ukmaker/nindasgym/assets/IMG_1002.jpg

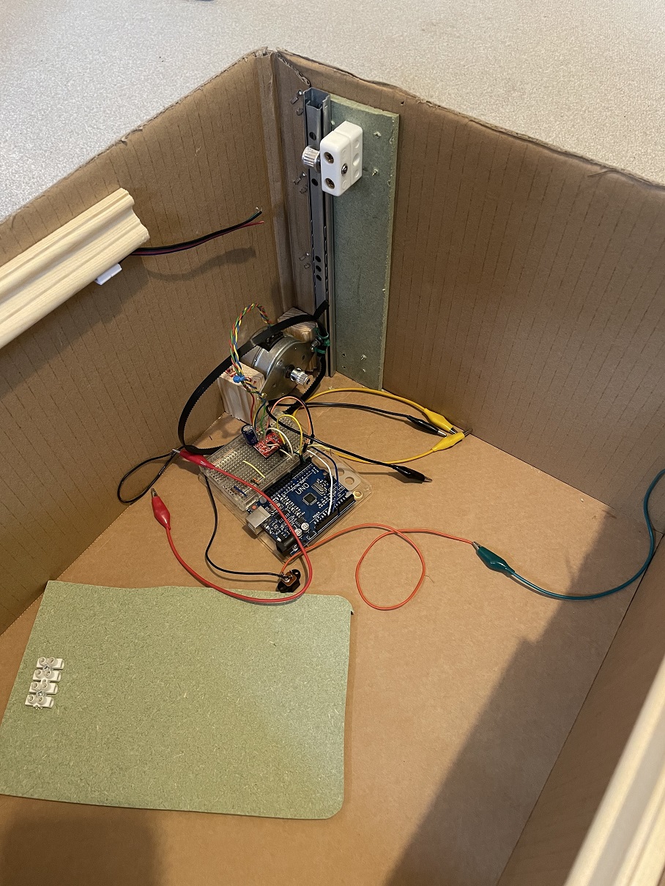
assets/IMG_1002.jpg
