ukmaker/nindasgym/assets/IMG_1003.jpg

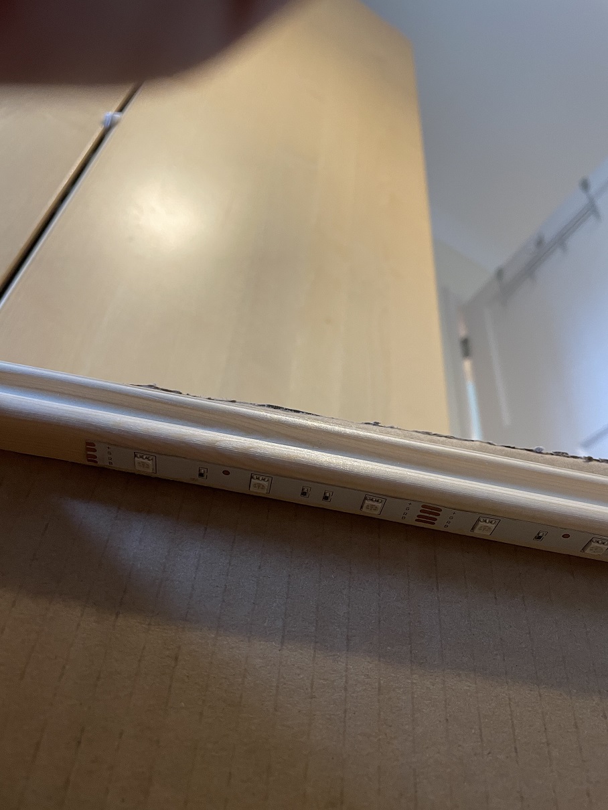
assets/IMG_1003.jpg
