ukmaker/nindasgym/assets/IMG_1004.jpg

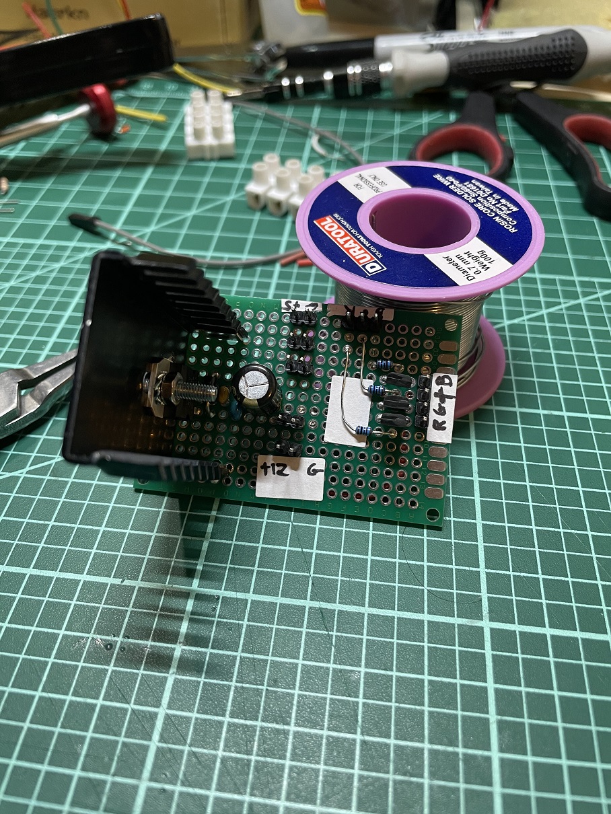
assets/IMG_1004.jpg
