ukmaker/nindasgym/assets/IMG_1005.jpg

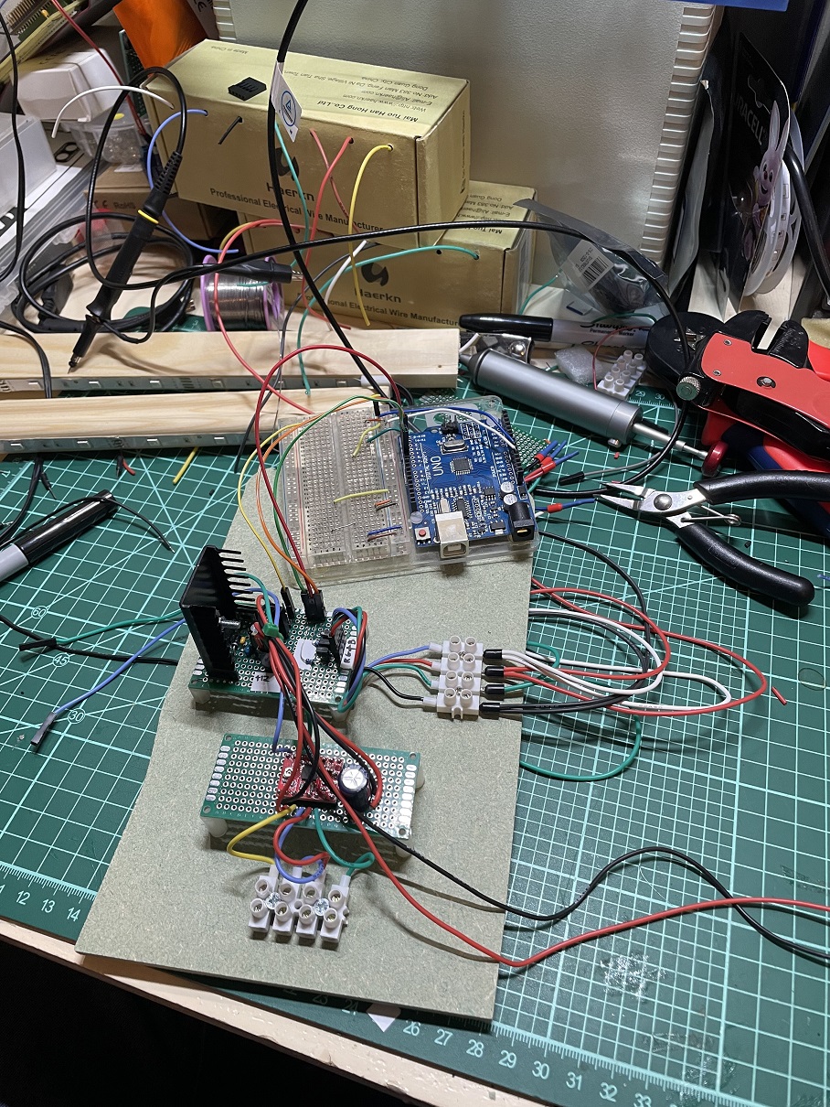
assets/IMG_1005.jpg
