ukmaker/nindasgym/assets/IMG_1007.jpg

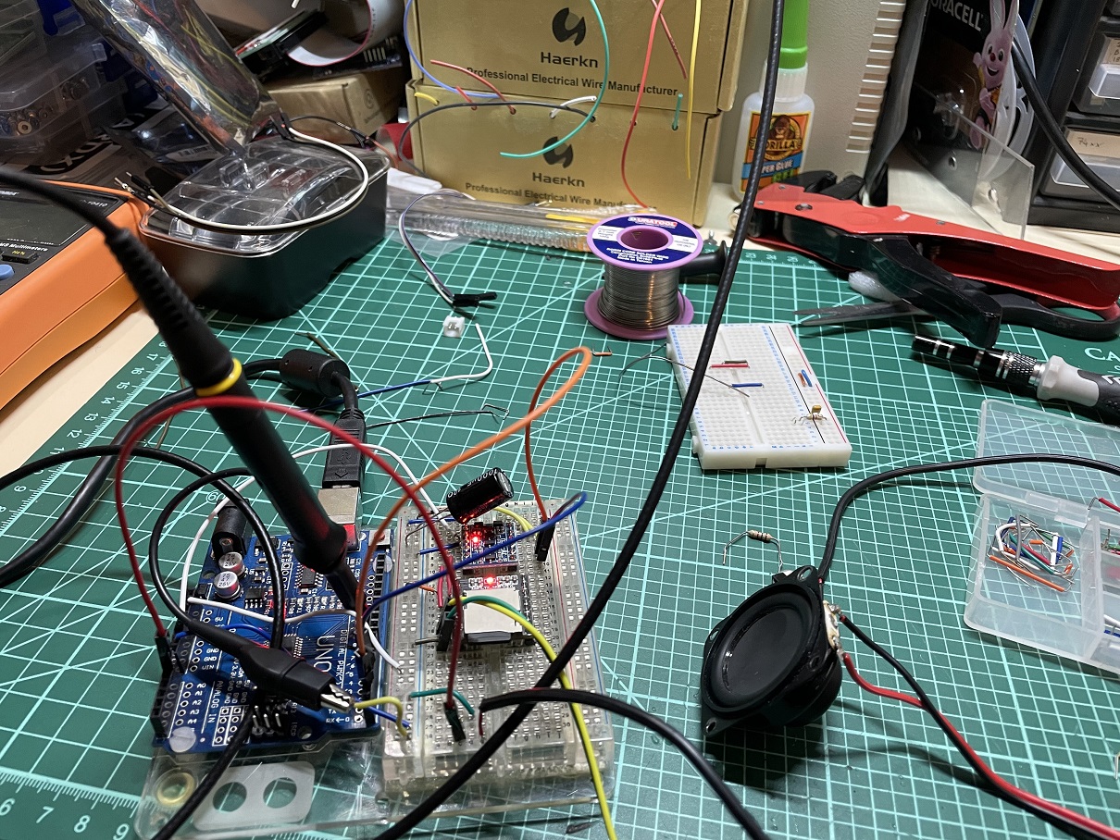
assets/IMG_1007.jpg
