ukmaker/nindasgym/assets/IMG_1008.jpg

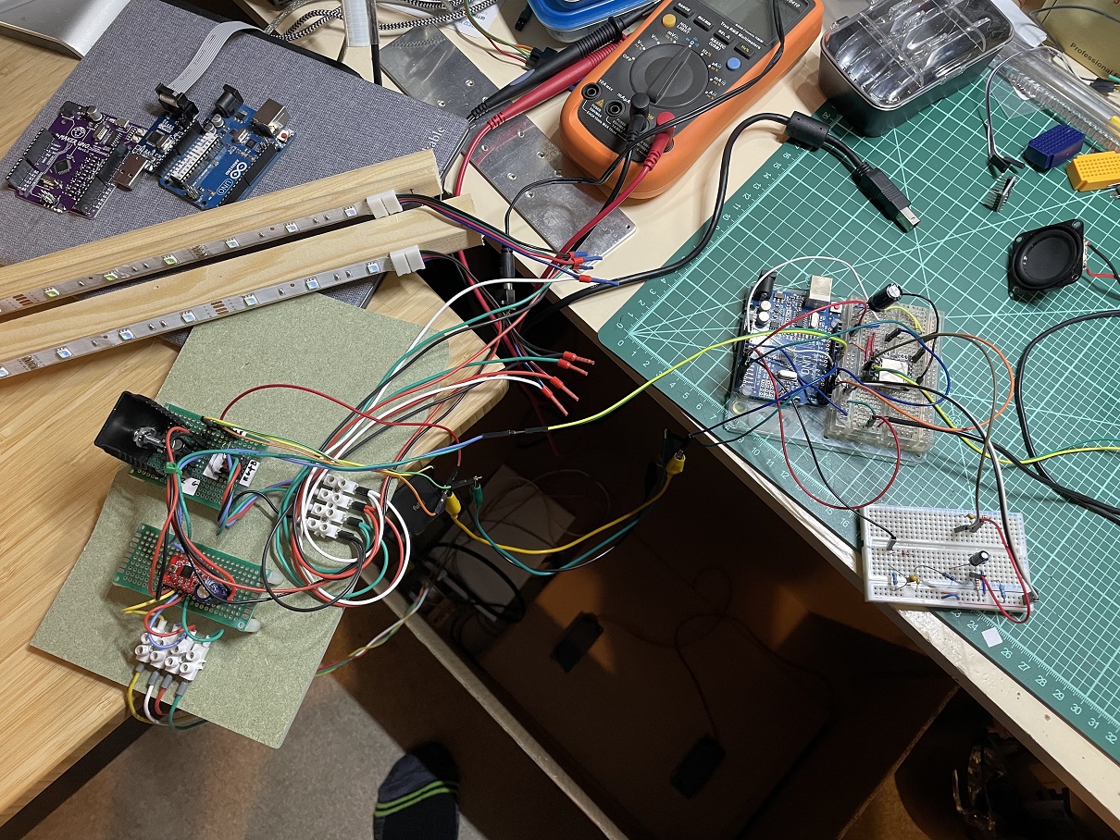
assets/IMG_1008.jpg
