ukmaker/nindasgym/assets/IMG_1011.jpg

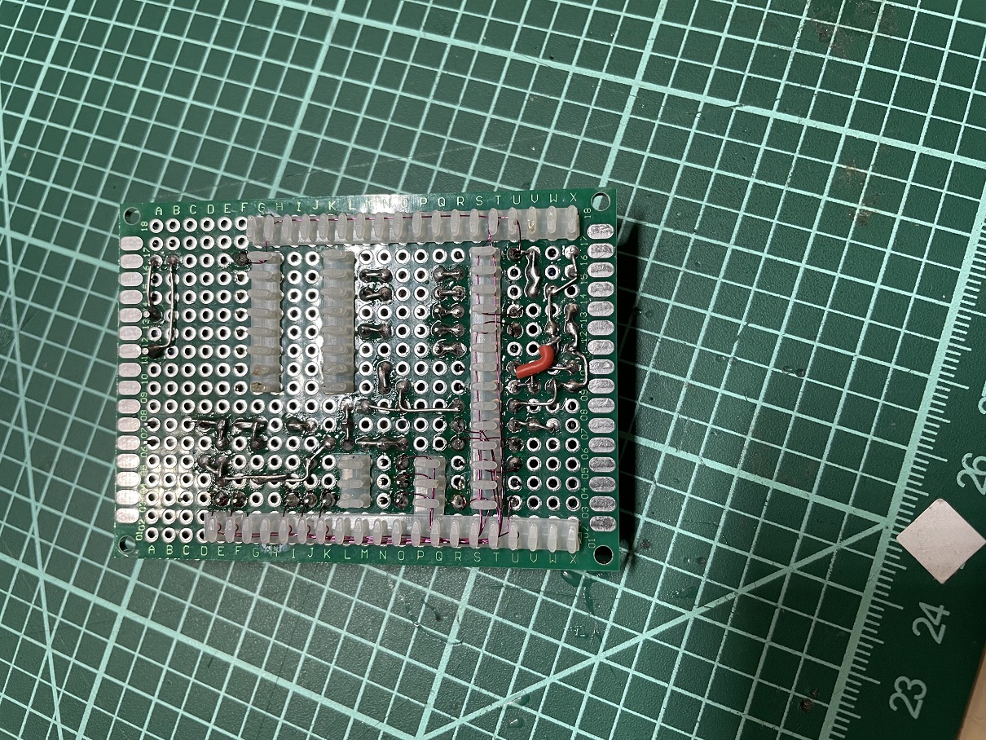
assets/IMG_1011.jpg
