ukmaker/nindasgym/assets/IMG_1012.jpg

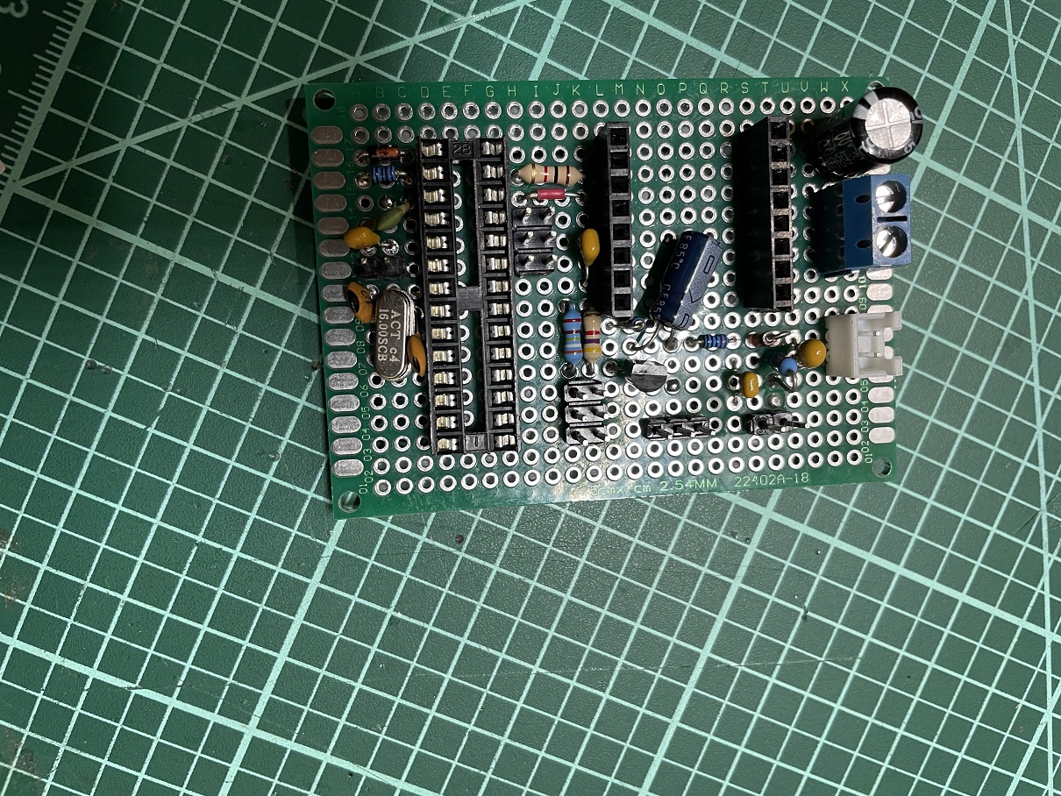
assets/IMG_1012.jpg
