ukmaker/nindasgym/assets/IMG_1013.jpg

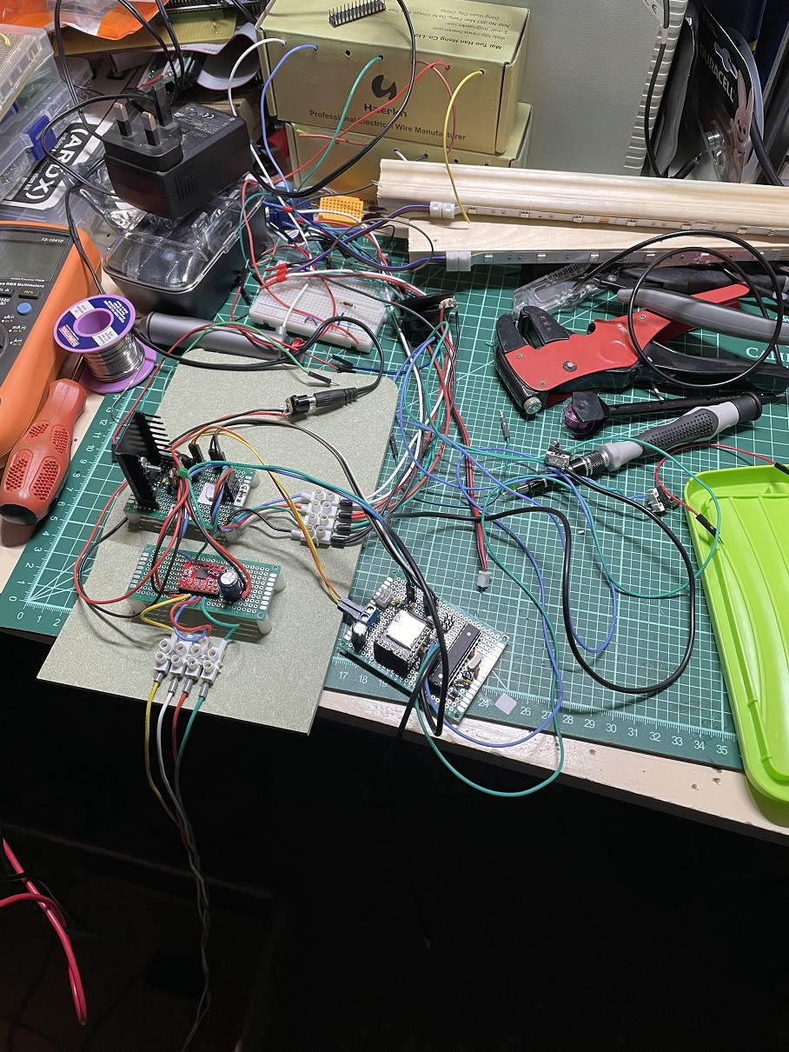
assets/IMG_1013.jpg
