ukmaker/nindasgym/assets/IMG_1023.JPG

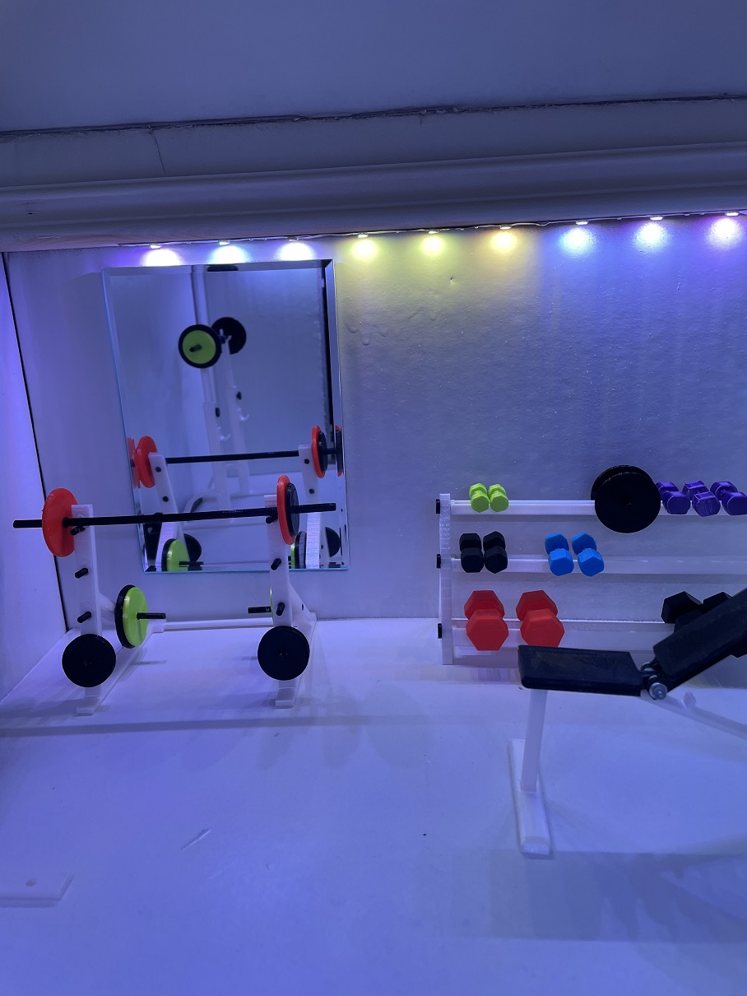
assets/IMG_1023.JPG
