ukmaker/nindasgym/assets/IMG_1027.JPG

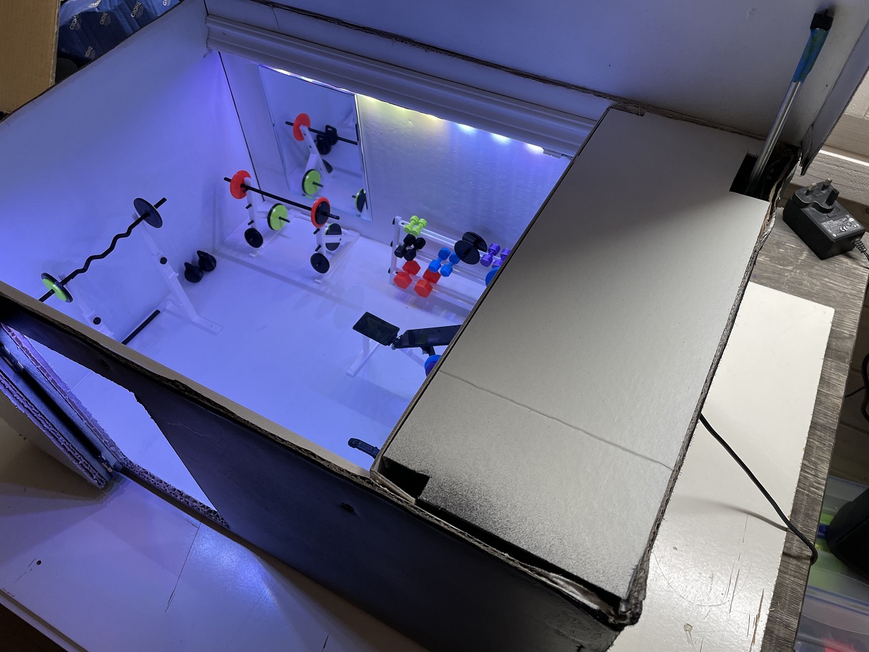
assets/IMG_1027.JPG
