ukmaker/nindasgym/assets/IMG_1028.JPG

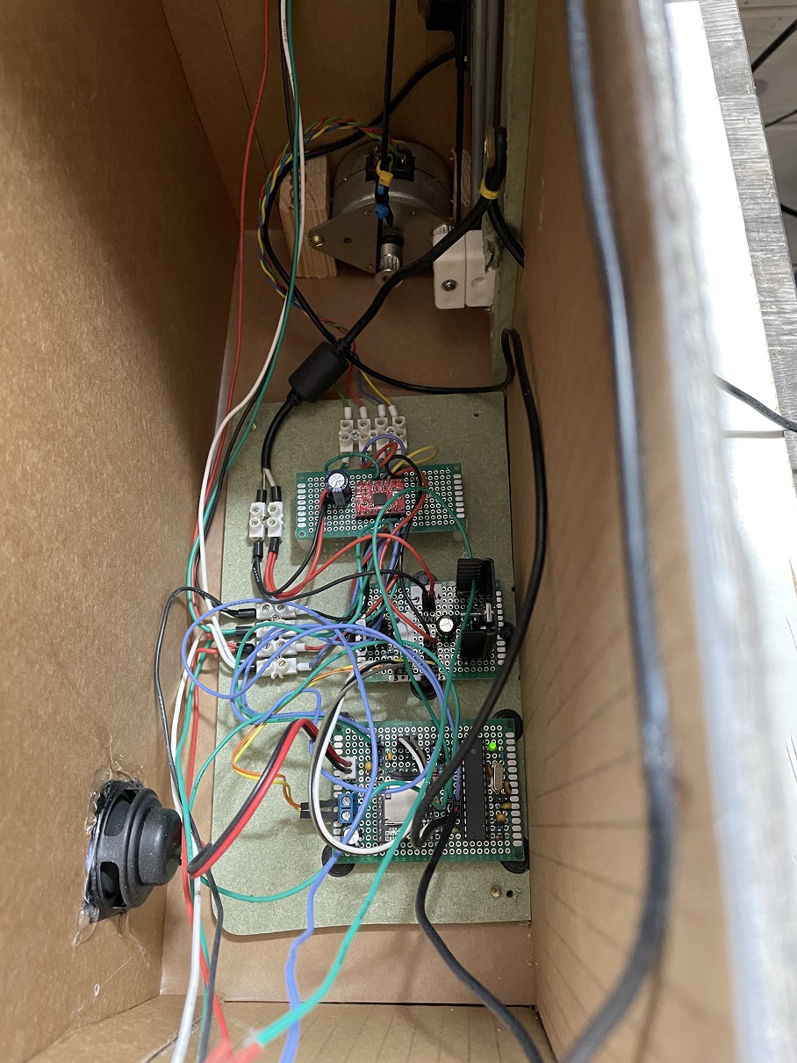
assets/IMG_1028.JPG
