ukmaker/nindasgym/assets/IMG_1029.jpg

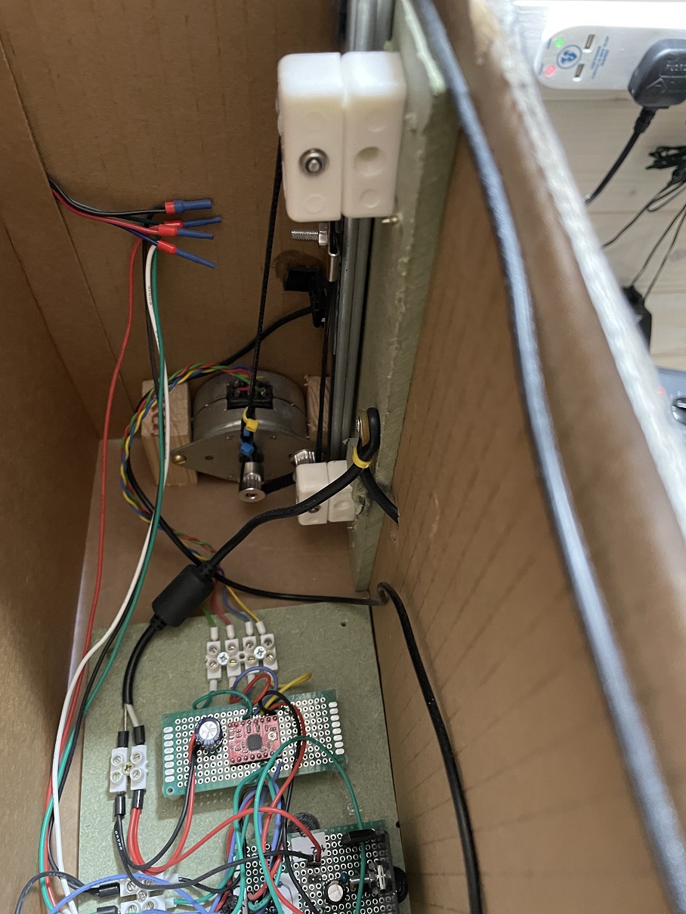
assets/IMG_1029.jpg
