ukmaker/nindasgym/Gym/PlayMp3/PlayMp3.ino

// this example will play a track and then 
// every five seconds play another track
//
// it expects the sd card to contain these three mp3 files
// but doesn't care whats in them
//
// sd:/mp3/0001.mp3
// sd:/mp3/0002.mp3
// sd:/mp3/0003.mp3

#include <DFMiniMp3.h>

// forward declare the notify class, just the name
//

#include <NeoSWSerial.h>
class Mp3Notify; 

// define a handy type using serial and our notify class
//
//typedef DFMiniMp3<HardwareSerial, Mp3Notify> DfMp3; 

// instance a DfMp3 object, 
//
//DfMp3 dfmp3(Serial1);

// Some arduino boards only have one hardware serial port, so a software serial port is needed instead.
// comment out the above definitions and use these
NeoSWSerial secondarySerial(11, 12); // RX, TX
typedef DFMiniMp3<NeoSWSerial, Mp3Notify, Mp3ChipMH2024K16SS> DfMp3;
 DfMp3 dfmp3(secondarySerial);

// implement a notification class,
// its member methods will get called 
//
class Mp3Notify
{
public:
  static void PrintlnSourceAction(DfMp3_PlaySources source, const char* action)
  {
    if (source & DfMp3_PlaySources_Sd) 
    {
        Serial.print("SD Card, ");
    }
    if (source & DfMp3_PlaySources_Usb) 
    {
        Serial.print("USB Disk, ");
    }
    if (source & DfMp3_PlaySources_Flash) 
    {
        Serial.print("Flash, ");
    }
    Serial.println(action);
  }
  static void OnError([[maybe_unused]] DfMp3& mp3, uint16_t errorCode)
  {
    // see DfMp3_Error for code meaning
    Serial.println();
    Serial.print("Com Error ");
    Serial.println(errorCode);
  }
  static void OnPlayFinished([[maybe_unused]] DfMp3& mp3, [[maybe_unused]] DfMp3_PlaySources source, uint16_t track)
  {
    Serial.print("Play finished for #");
    Serial.println(track);  
  }
  static void OnPlaySourceOnline([[maybe_unused]] DfMp3& mp3, DfMp3_PlaySources source)
  {
    PrintlnSourceAction(source, "online");
  }
  static void OnPlaySourceInserted([[maybe_unused]] DfMp3& mp3, DfMp3_PlaySources source)
  {
    PrintlnSourceAction(source, "inserted");
  }
  static void OnPlaySourceRemoved([[maybe_unused]] DfMp3& mp3, DfMp3_PlaySources source)
  {
    PrintlnSourceAction(source, "removed");
  }
};

void setup() 
{
  Serial.begin(115200);

  Serial.println("initializing...");
  
  dfmp3.begin();

  uint16_t volume = dfmp3.getVolume();
  Serial.print("volume ");
  Serial.println(volume);
  dfmp3.setVolume(24);
  
  uint16_t count = dfmp3.getTotalTrackCount(DfMp3_PlaySource_Sd);
  Serial.print("files ");
  Serial.println(count);
  
  Serial.println("starting...");

    Serial.println("track 1"); 
  dfmp3.playMp3FolderTrack(1);  // sd:/mp3/0001.mp3
}

void waitMilliseconds(uint16_t msWait)
{
  uint32_t start = millis();
  
  while ((millis() - start) < msWait)
  {
    // if you have loops with delays, its important to 
    // call dfmp3.loop() periodically so it allows for notifications 
    // to be handled without interrupts
    dfmp3.loop(); 
    delay(1);
  }
}

void loop() 
{

  
 /* waitMilliseconds(5000);
  
  Serial.println("track 2"); 
  dfmp3.playMp3FolderTrack(1); // sd:/mp3/0002.mp3
  
  waitMilliseconds(5000);
  
  Serial.println("track 3");
  dfmp3.playMp3FolderTrack(3); // sd:/mp3/0002.mp3
  
  waitMilliseconds(5000); */
}
